RetroStack/TRS-80-Model-I-Parts/Keyboard_Spacebar_Clip/Images/IMG_1189_Small.png

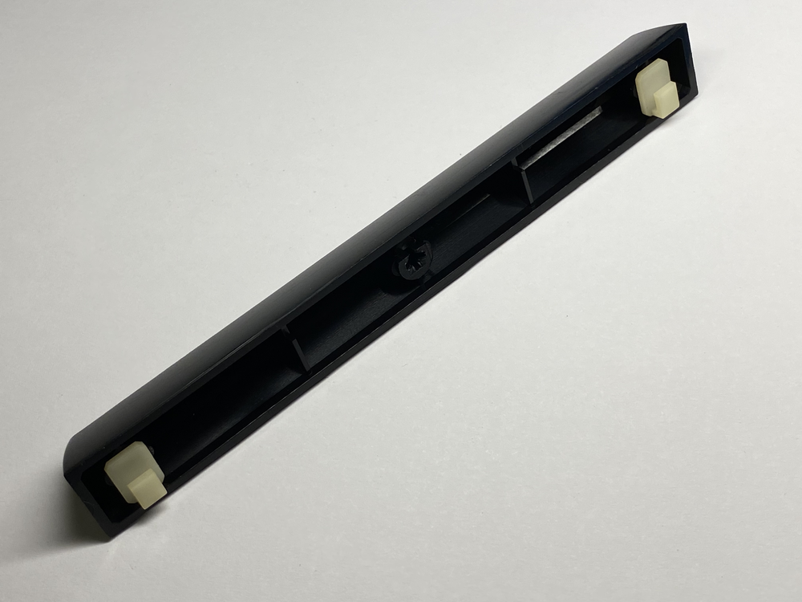
Keyboard_Spacebar_Clip/Images/IMG_1189_Small.png
