RetroStack/TRS-80-Model-I-Parts/Keyboard_Clip/Keyboard_Clip.stl

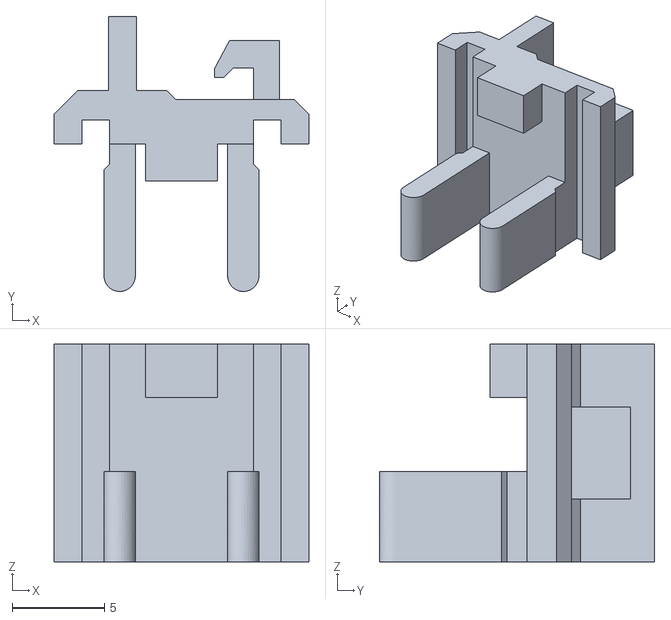
[picture p150: CAD file, 2024-01-02]
Keyboard_Clip/Keyboard_Clip.stl
13.8 x 14.9 x 11.8
