RetroStack/TRS-80-Model-I-Parts/Keyboard_Stem_ALPS/Keyboard_Stem_ALPS.stl

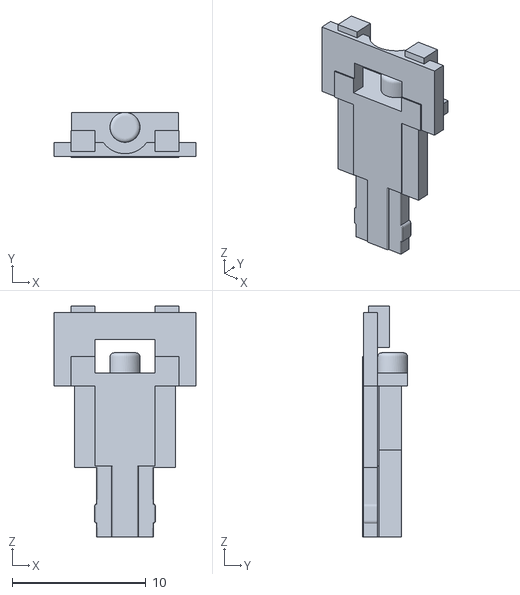
[picture p152: CAD file, 2024-01-22]
Keyboard_Stem_ALPS/Keyboard_Stem_ALPS.stl
10.6 x 3.40 x 17.3
