RetroStack/TRS-80-Model-I-Parts/Main_Enclosure/Bottom_Mini.stl

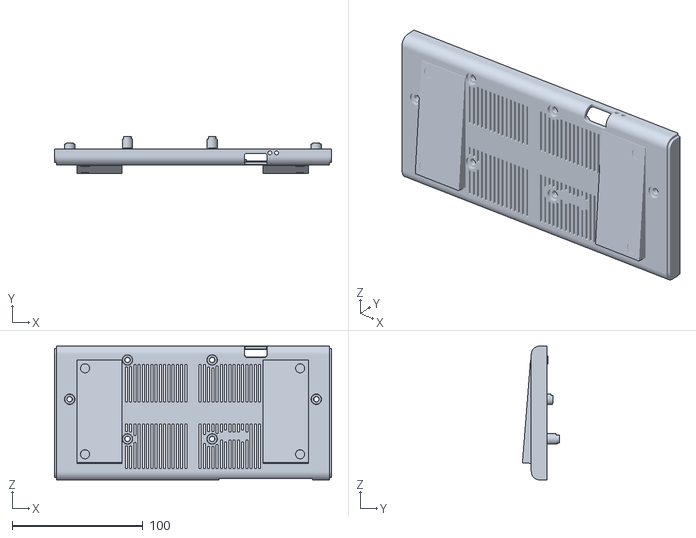
[picture p153: CAD file, 2024-08-23]
Main_Enclosure/Bottom_Mini.stl
212.0 x 28.5 x 102.5
