RetroStack/TRS-80-Model-I-Parts/Keyboard_Clip/Keyboard_Clip_Printable.stl

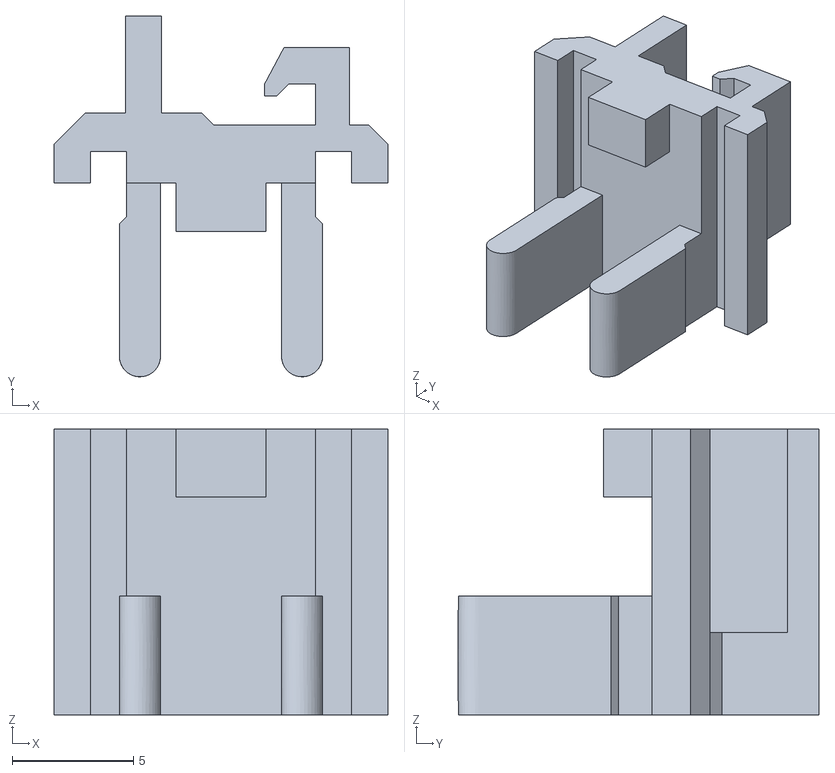
[picture p154: CAD file, 2024-01-02]
Keyboard_Clip/Keyboard_Clip_Printable.stl
13.8 x 14.9 x 11.8
