RetroStack/TRS-80-Model-I-Parts/Keyboard_Spacebar_Clip/Keyboard_Spacebar_Clip.stl

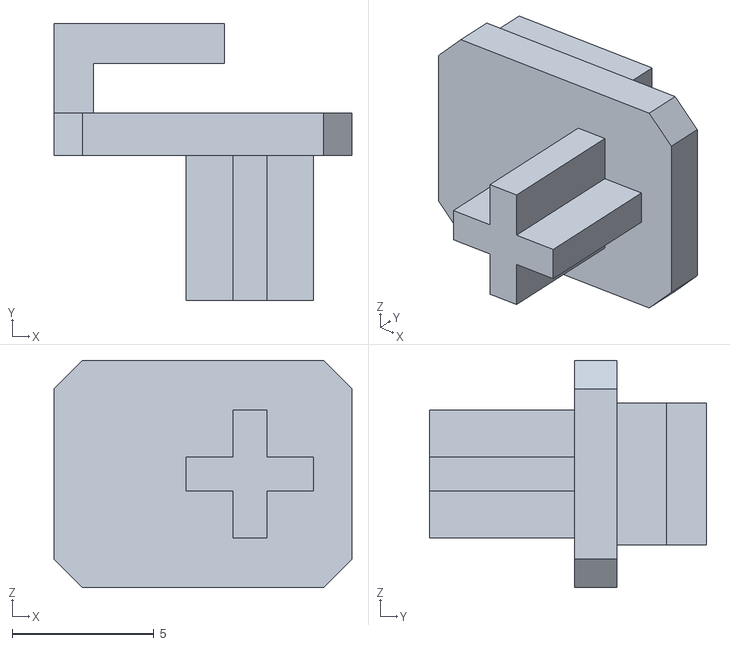
[picture p155: CAD file, 2024-01-22]
Keyboard_Spacebar_Clip/Keyboard_Spacebar_Clip.stl
10.5 x 9.75 x 8.00
