RetroStack/TRS-80-Model-I-Parts/Keyboard_Stem_ALPS/Keyboard_Stem_ALPS_Printable.stl

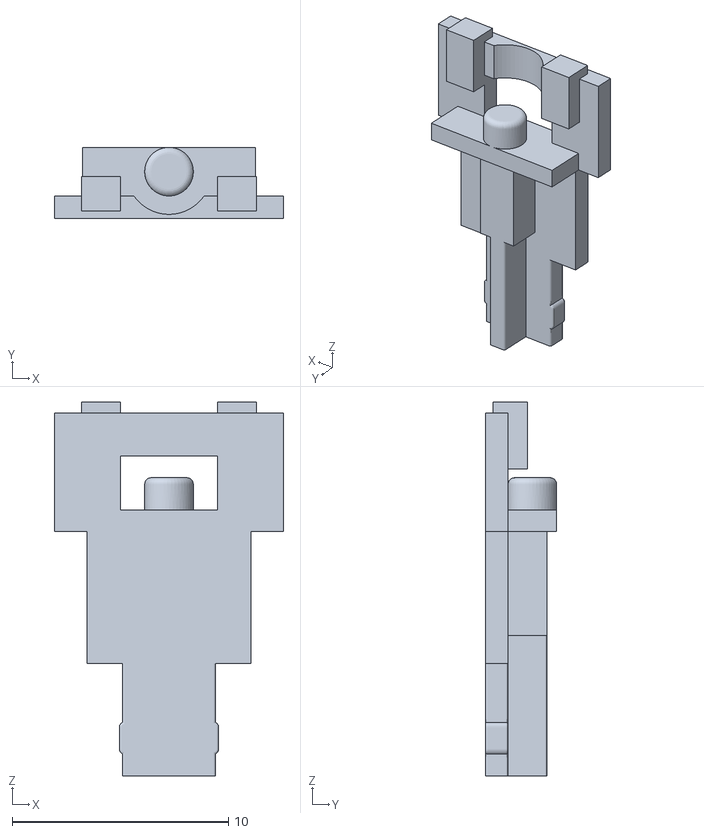
[picture p156: CAD file, 2024-01-22]
Keyboard_Stem_ALPS/Keyboard_Stem_ALPS_Printable.stl
10.6 x 3.30 x 17.3
