RetroStack/TRS-80-Model-I-Parts/Main_Enclosure/Bottom_Left_Foot.stl

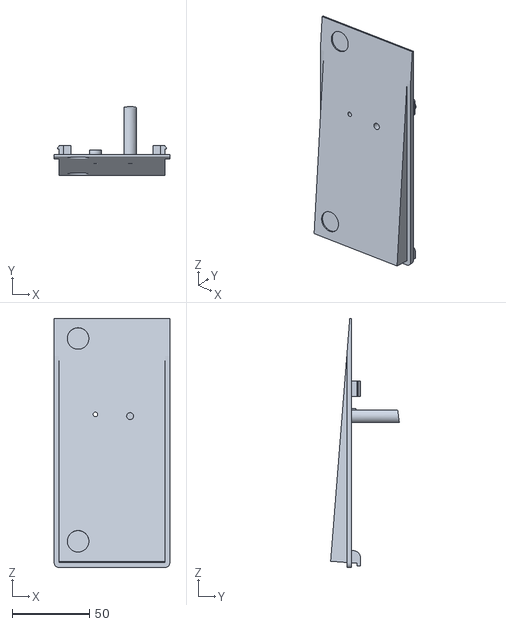
[picture p157: CAD file, 2024-05-24]
Main_Enclosure/Bottom_Left_Foot.stl
75.0 x 44.6 x 161.6
