RetroStack/TRS-80-Model-I-Parts/Main_Enclosure/Bottom_Right.stl

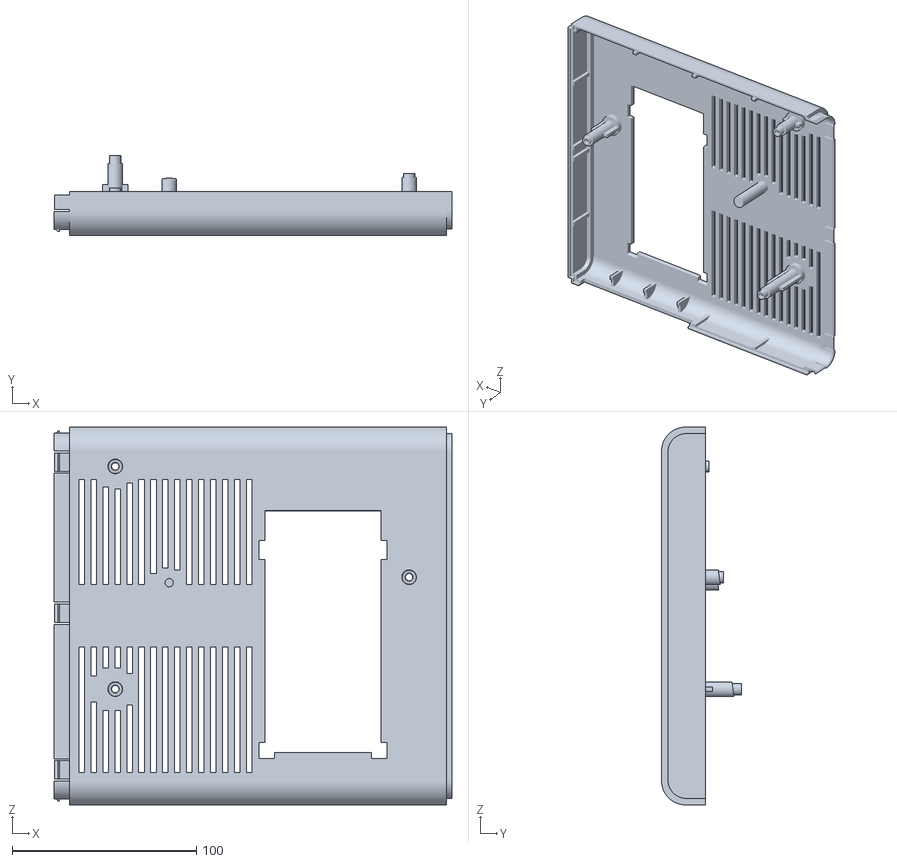
[picture p158: CAD file, 2024-05-24]
Main_Enclosure/Bottom_Right.stl
216.0 x 43.4 x 205.0
