RetroStack/TRS-80-Model-I-Parts/Main_Enclosure/Bottom_Right_Foot.stl

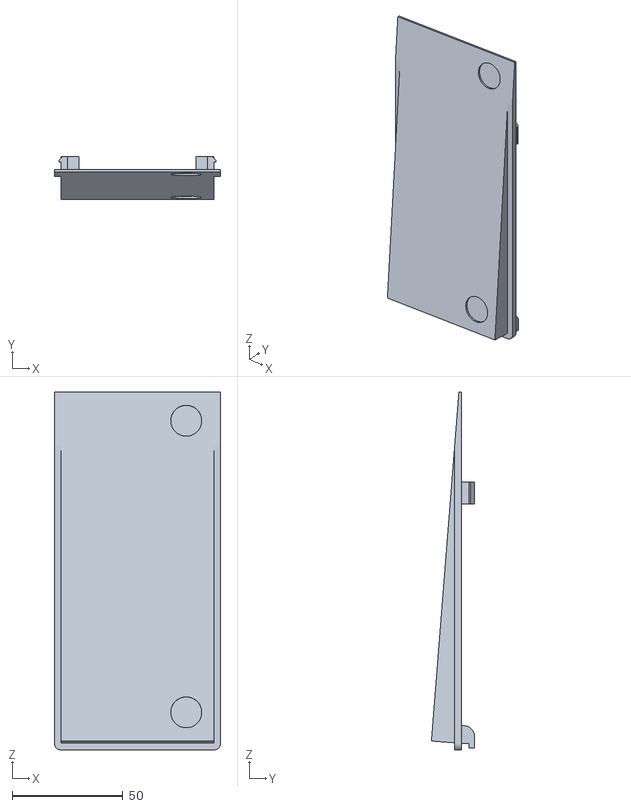
[picture p160: CAD file, 2024-05-24]
Main_Enclosure/Bottom_Right_Foot.stl
75.0 x 19.5 x 161.6
