RetroStack/TRS-80-Model-I-Parts/Main_Enclosure/Top_Left.stl

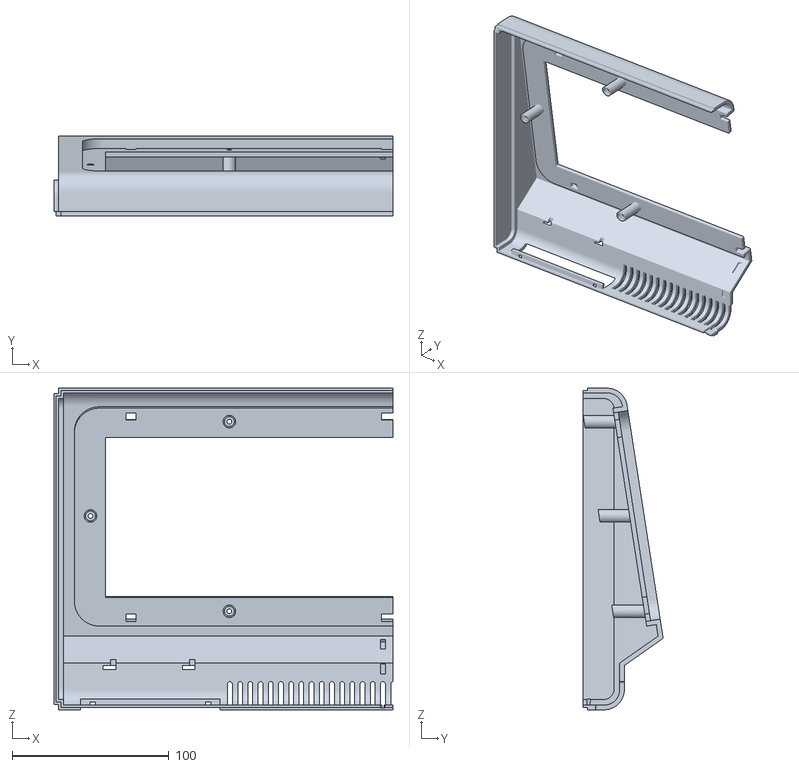
[picture p161: CAD file, 2024-05-24]
Main_Enclosure/Top_Left.stl
216.0 x 51.2 x 205.0
