RetroStack/TRS-80-Model-I-Parts/Main_Enclosure/Improved_Bottom.stl

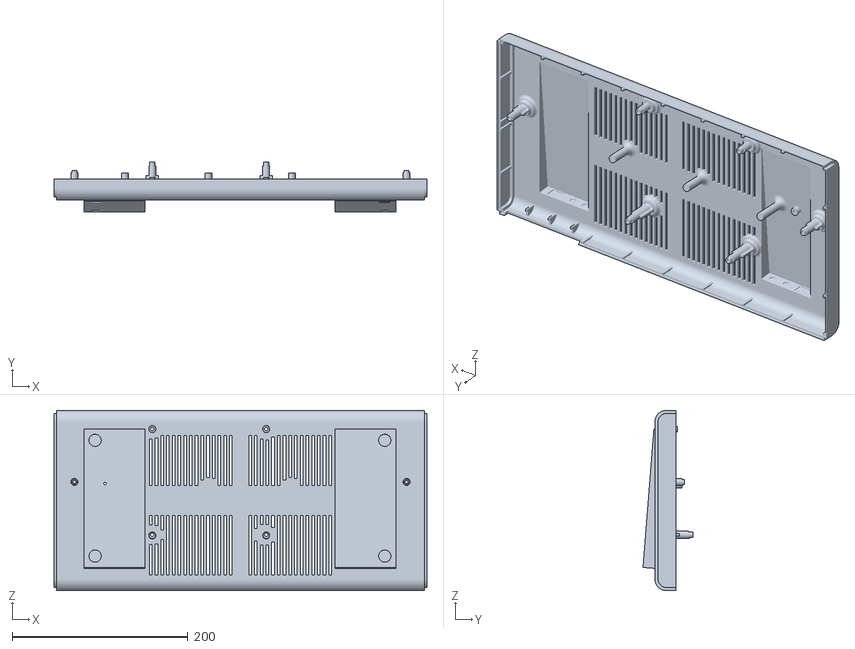
[picture p162: CAD file, 2024-05-20]
Main_Enclosure/Improved_Bottom.stl
424.0 x 56.9 x 205.0
