RetroStack/TRS-80-Model-I-Parts/Main_Enclosure/Original_Top.stl

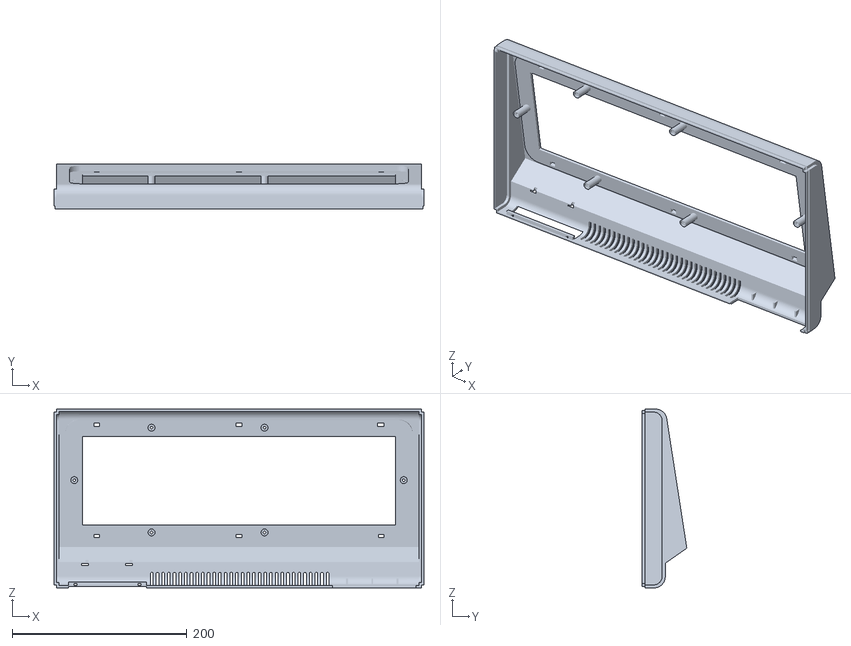
[picture p163: CAD file, 2024-05-20]
Main_Enclosure/Original_Top.stl
424.0 x 51.2 x 205.0
